FranzKugler/QlockThreeW32/src/LedDriverWS2812FastLED.cpp

/**
 * LedDriverWS2812FastLED
 * Implementation based on WS2812B strips, as used by the Adafruit NeoPixels.
 *
 * Adafruit's UeberGuide is well worth reading:
 * https://learn.adafruit.com/adafruit-neopixel-uberguide/overview
 *
 * @mc       ESP32S3
 * @author   Christian Aschoff / caschoff _AT_ mac _DOT_ com
 * @version  2.0
 * @created  5.1.2015
 * @updated  15.8.2026
 *
 * Version history:
 * V 1.0:  - Created.
 * V 1.1:  - Brightness getter brought in line.
 * V 1.2:  - Removed support for the old Arduino IDE (up to 1.0.6).
 * V 2.0:  - Consolidated for ESP32-S3 / WS2812B, comments translated to English.
 *
 * Wiring, from the owner of the clock and confirmed against the code and then
 * against the strip itself:
 *
 *     index 0    bottom right  (the R of the German panel)
 *     ...        meandering left, then up one row and back to the right
 *     index 109  top right     (the F)
 *     110..113   the corners: bottom right, top right, top left, bottom left
 *
 * This comment used to say "fed in at the top left, then serpentine downwards"
 * with the corners in a fourth order again, and all of it was wrong while the
 * code beneath it was right. It is restated here now because physicalFor()
 * gives the mapping a single home and /lab lets any claim about it be checked
 * in seconds - lighting cell (9,10) and lighting pixel 0 have to be the same
 * lamp, and now they can be seen to be.
 *
 * Which frame buffer row is which corner is still a separate question, because
 * the path there passes through _setPixel(), which swaps 110 with 112 on top
 * of the mapping in writeScreenBufferToMatrix. That one is written down at
 * Renderer::setCorners, from having been watched on the clock.
 *
 */
#include "LedDriverWS2812FastLED.h"

// #define DEBUG
// #include "Debug.h"

// Debug and the debugX macros, plus the ring the web UI reads them out of.
#include "LogBuffer.h"

#define NUM_PIXEL 114

/*
 * The four corner LEDs, named by where they are on the face rather than by
 * where they sit on the strip. Which frame buffer row is which corner is
 * written down at Renderer::setCorners and comes from the clock; these are
 * that mapping followed through _setPixel(), which swaps 110 with 112:
 *
 *     matrix[1] top left      -> _setPixel(110) -> _leds[112]
 *     matrix[0] top right     -> _setPixel(111) -> _leds[111]
 *     matrix[3] bottom right  -> _setPixel(112) -> _leds[110]
 *     matrix[2] bottom left   -> _setPixel(113) -> _leds[113]
 *
 * Only the coloured corners need them: that mode writes the pixels itself
 * instead of going through the frame buffer, so it has no rows to read.
 */
#define CORNER_TOP_LEFT     112
#define CORNER_TOP_RIGHT    111
#define CORNER_BOTTOM_RIGHT 110
#define CORNER_BOTTOM_LEFT  113

// The colour a corner settles on once the next one has lit; the newest one
// is the one that moves. Violet, on FastLED's rainbow wheel - which runs
// blue to purple over 160..191, not the cyan a geometric HSV would give.
//
// Note that the moving corner ends its minute at 3*59 = 177, just short of
// this, so in the last seconds of a minute the newest corner and the
// settled ones are nearly the same colour. That is how this mode has
// always behaved and is left alone.
#define CORNER_SETTLED_HUE 180

#ifndef LED_OUTPUT_PIN
	#define LED_OUTPUT_PIN 2
#endif

/**
 * Initialisation.
 *
 * @param data pin the data line is attached to.
 */
LedDriverWS2812FastLED::LedDriverWS2812FastLED(void)
{
	_leds = (CRGB*)malloc(NUM_PIXEL*sizeof(CRGB));
	//FastLED.addLeds<NEOPIXEL, 16>(_leds, NUM_PIXEL);
	
	FastLED.addLeds<NEOPIXEL, LED_OUTPUT_PIN>(_leds, NUM_PIXEL);
	FastLED.setMaxPowerInVoltsAndMilliamps(5, 2500);

	setColor(250, 255, 200);
	setColorCorners(false, true);
	updateFunkStatus(0);
}

/**
 * init() is called from the main program's init().
 * The LED driver should be brought into a defined
 * initial state here.
 */
/*
 * What the supply can give, minus room for the ESP32 and its radio.
 *
 * 114 WS2812B on white at full scale want about 6.8 A, which no sensible
 * supply for this clock provides - the normal face lights a fraction of them,
 * so it never comes up, but the lab interface can address every pixel and
 * would walk straight into it.
 *
 * Know how the cap works before trusting a measurement taken near it: FastLED
 * enforces it by scaling the *global* brightness down, so a frame over budget
 * is not the frame that was asked for. That is why /lab reports the estimated
 * draw beside every reading rather than only capping and staying quiet.
 */
#define SUPPLY_VOLTS 5
// 2.5 A of a 5 A supply. Measured: the normal face draws about 170 mA, so this
// never engages in use - it is a backstop against a lab frame, and it is set
// this low because 4 A was not: the first whole-face white frame browned the
// clock out and reset it. The real protection is LAB_MAX_DRAW_MW, which
// refuses such a frame instead of dimming it.
#define SUPPLY_MILLIAMPS 2500

void LedDriverWS2812FastLED::init()
{
	FastLED.setMaxPowerInVoltsAndMilliamps(SUPPLY_VOLTS, SUPPLY_MILLIAMPS);
	setBrightness(50);
	clearData();
	wakeUp();
}

void LedDriverWS2812FastLED::printSignature()
{
	debugI("FastLED - WS2812B on Pin %d\n", LED_OUTPUT_PIN);
}

/**
 * Write the frame buffer to the LED matrix.
 *
 * @param onChange TRUE if the frame buffer changed,
 *                  FALSE if this was a refresh call.
 */
void LedDriverWS2812FastLED::writeScreenBufferToMatrix(word matrix[16], boolean onChange)
{
	if (onChange || _dirty)
	{
		_dirty = false;
		FastLED.clear();

		CRGB color = CRGB(_brightnessScaleColor(getRed()), _brightnessScaleColor(getGreen()), _brightnessScaleColor(getBlue()));

		for (byte y = 0; y < 10; y++)
		{
			for (byte x = 5; x < 16; x++)
			{
				word t = 1 << x;
				if ((matrix[y] & t) == t)
				{
					_setPixel(15 - x, y, color);
				}
			}
		}

		if (!_colorCorners)
		{
			// The corner rows carry no letters, so they are handed to _setPixel
			// whole rather than column by column. Which row is which corner is
			// stated at Renderer::setCorners; the numbers below only have to
			// agree with it, and were checked against the clock.
			if ((matrix[1] & 0b0000000000011111) == 0b0000000000011111)
			{
				_setPixel(110, color); // top left
			}
			if ((matrix[0] & 0b0000000000011111) == 0b0000000000011111)
			{
				_setPixel(111, color); // top right
			}
			if ((matrix[3] & 0b0000000000011111) == 0b0000000000011111)
			{
				_setPixel(112, color); // bottom right
			}
			if ((matrix[2] & 0b0000000000011111) == 0b0000000000011111)
			{
				_setPixel(113, color); // bottom left
			}
		}
		else
		{
			/*
			 * The coloured corners. What each one shows is cornerHue()'s to
			 * say - this only puts it on the strip, at the same gamma the
			 * letters get.
			 *
			 * It cannot go through the frame buffer, because the hue differs
			 * per corner and a row of that buffer is one bit.
			 */
			const byte PIXEL[4] = {
				CORNER_TOP_LEFT, CORNER_TOP_RIGHT, CORNER_BOTTOM_RIGHT, CORNER_BOTTOM_LEFT
			};

			for (byte corner = 0; corner < 4; corner++)
			{
				byte hue;
				_leds[PIXEL[corner]] = cornerHue(corner, hue)
					? CHSV(hue, 255, _brightnessScaled)
					: CHSV(0, 0, 0);
			}
		}

		if (_funkStatus)
		{
			int brightness = _brightnessScaled;  // same gamma as the letters
			if ((_funkStatus & 0x0F) == 1)
				color = CHSV(96, 255, brightness); 
			else if ((_funkStatus & 0x0F) == 2)
				color = CHSV(0, 255, brightness); 
			else
				color = CHSV(0,0,0);
				
			if ((_funkStatus & 0x80) && (_second % 2))
				color = CHSV(0,0,0);

			_setPixel(3, 3, color);
			_setPixel(4, 3, color);
			_setPixel(5, 3, color);
			_setPixel(6, 3, color);
		}
		FastLED.show();
	}
}

void LedDriverWS2812FastLED::updateFunkStatus(byte status)
{
	_funkStatus = status;
}

/**
* Adjust the display colour.
*
* @param hue Hue
* @param sat Sat
*/
void LedDriverWS2812FastLED::setColorHS(byte hue, byte sat)
{
	CRGB pixel = CHSV(hue, sat, 255);
	setColor(pixel.r, pixel.g, pixel.b);
}


/**
 * Adjust the display brightness.
 *
 * @param brightnessInPercent the brightness.
 */
void LedDriverWS2812FastLED::setBrightness(byte brightnessInPercent)
{
	if (brightnessInPercent != _brightnessInPercent)
	{
		_brightnessInPercent = brightnessInPercent;
		_brightnessScaled = _gammaScale(brightnessInPercent);
		_dirty = true;
	}
}

/**
 * The setting as a drive value, with gamma.
 *
 * Perceived brightness follows roughly a power law, so driving the LEDs
 * proportionally to the setting does not feel proportional: half way up the
 * slider looked far brighter than half, and everything interesting happened in
 * the bottom third. Raising the setting to 2.2 spreads the useful range over
 * the whole slider.
 *
 * The floor matters as much as the curve: without it a setting of 1 to 3 per
 * cent rounds to zero and the clock goes dark while the web UI says it is on.
 */
byte LedDriverWS2812FastLED::_gammaScale(byte percent)
{
	if (percent == 0) return 0;
	if (percent >= 100) return 255;

	long value = lroundf(255.0f * powf(percent / 100.0f, 2.2f));
	if (value < 1) value = 1;
	return (byte)value;
}

/**
 * Get the current brightness.
 */
byte LedDriverWS2812FastLED::getBrightness()
{
	return _brightnessInPercent;
}

/**
 * Adjust the size of the frame buffer.
 *
 * @param linesToWrite how many rows of the frame buffer
 *                     should be written?
 */
void LedDriverWS2812FastLED::setLinesToWrite(byte linesToWrite)
{}

/**
 * Switch the display off.
 */
void LedDriverWS2812FastLED::shutDown()
{
	FastLED.clear();
	FastLED.show();
}

/**
 * Switch the display on.
 */
void LedDriverWS2812FastLED::wakeUp()
{}

/**
 * Clear the LED driver's data.
 */
void LedDriverWS2812FastLED::clearData()
{
	FastLED.clear();
	FastLED.show();
}

/**
 * Set a pixel in the matrix by x/y coordinate.
 */
void LedDriverWS2812FastLED::_setPixel(byte x, byte y, CRGB c)
{
	_setPixel((10 - x) + 11 * (9 - y), c);
}

/**
 * Where a letter cell sits on the strip - the wiring, worked out once.
 *
 * This is the same arithmetic _setPixel() does in two steps, gathered into one
 * place because the lab interface has to answer "which pixel is cell (r,c)"
 * and because the wiring had been described wrongly in three files. It is not
 * derived from the comment that used to sit at the top of this file; it is the
 * code that has always been driving the clock, checked against the owner's
 * description of the strip:
 *
 *     index 0   bottom right   ("R" on the German panel)
 *     ...       meandering left, then up one row and back to the right
 *     index 109 top right      ("F")
 *     110..113  the corners: bottom right, top right, top left, bottom left
 */
byte LedDriverWS2812FastLED::physicalFor(byte row, byte col)
{
	if (row > 9 || col > 10) return 255;

	// Reading order to strip order: the first cell is the bottom right one.
	byte num = (byte)((10 - col) + 11 * (9 - row));

	// Every other row runs the other way, which is what "meander" means.
	if ((num / 11) % 2 == 0) return num;
	return (byte)(((num / 11) * 11) + 10 - (num % 11));
}

void LedDriverWS2812FastLED::setPixelRaw(byte index, CRGB colour)
{
	if (index >= NUM_PIXEL) return;
	_leds[index] = colour;
}

CRGB LedDriverWS2812FastLED::getPixelRaw(byte index) const
{
	if (index >= NUM_PIXEL) return CRGB::Black;
	return _leds[index];
}

void LedDriverWS2812FastLED::clearRaw()
{
	for (byte i = 0; i < NUM_PIXEL; i++) _leds[i] = CRGB::Black;
}

void LedDriverWS2812FastLED::showRaw()
{
	// Marked dirty so that leaving the lab redraws the face from the frame
	// buffer even if nothing else changed in the meantime.
	_dirty = true;
	FastLED.show();
}

uint32_t LedDriverWS2812FastLED::estimatedDrawMilliwatts() const
{
	return calculate_unscaled_power_mW(_leds, NUM_PIXEL);
}

/**
 * Set a pixel in the strip (the corner LEDs come last).
 */
boolean LedDriverWS2812FastLED::cornerHue(byte corner, byte &hue) const
{
	/*
	 * What one corner shows in the coloured-corner mode, by its place on the
	 * face: 0 top left, 1 top right, 2 bottom right, 3 bottom left. That is
	 * reading order, and reading order is clockwise, so the order the corners
	 * light in is 0,1,2,3 one way and 1,0,3,2 the other - the same two
	 * sequences Renderer::setCorners uses, and for the same reason. Where a
	 * frame buffer row is which corner is written down there.
	 *
	 * The newest corner walks the hue wheel with the seconds and the ones
	 * before it sit still, so the moving one says roughly how far into the
	 * minute the clock is: red at :00 through to blue at :59.
	 *
	 * This is the answer to "what colour is that corner", and both askers get
	 * it from here - the strip, and GET /panel for the web UI's preview. The
	 * preview showed the plain display colour for a long time because it had
	 * no way to ask; a second implementation in the browser would have been
	 * the wrong fix.
	 *
	 * It counts the same minutes Renderer::setCorners does, which the hand
	 * written switch this replaced did not: a remainder of 0 lit a corner, so
	 * every corner came on a minute early and the fourth never went out.
	 */
	const byte CLOCKWISE[4]         = { 0, 1, 2, 3 };
	const byte COUNTER_CLOCKWISE[4] = { 1, 0, 3, 2 };
	const byte *order = _cw ? CLOCKWISE : COUNTER_CLOCKWISE;

	byte lit = _minute % 5;

	for (byte step = 0; step < 4; step++)
	{
		if (order[step] != corner) continue;

		if (step + 1 > lit) return false;                       // not yet
		hue = (step + 1 == lit) ? (byte)(3 * _second)           // the newest
		                        : (byte)CORNER_SETTLED_HUE;     // and settled
		return true;
	}

	return false;
}

void LedDriverWS2812FastLED::_setPixel(byte num, CRGB c)
{
	if (num < 110)
	{
		if ((num / 11) % 2 == 0)
		{
			_leds[num] = c;
		}
		else
		{
			_leds[((num / 11) * 11) + 10 - (num % 11)] = c;
		}
	}
	else
	{
		switch (num)
		{
		case 110:
			_leds[112] = c;
			break;
		case 111:
			_leds[111] = c;
			break;
		case 112:
			_leds[110] = c;
			break;
		case 113:
			_leds[113] = c;
			break;
		}
	}
}

/**
 * Function for clean 'rainbow' colours.
 * Copied from the Adafruit examples (strand).
 */
uint32_t LedDriverWS2812FastLED::_wheel(byte wheelPos)
{
	return 0;
}

/**
 * Helper for scaling the colours.
 */
byte LedDriverWS2812FastLED::_brightnessScaleColor(byte colorPart)
{
	return (byte)(((int)colorPart * (int)_brightnessScaled + 127) / 255);
}

void LedDriverWS2812FastLED::setColor(byte red, byte green, byte blue) {
    _red = red;
    _green = green;
    _blue = blue;
}

byte LedDriverWS2812FastLED::getRed() {
    return _red;
}

byte LedDriverWS2812FastLED::getGreen() {
    return _green;
}

byte LedDriverWS2812FastLED::getBlue() {
    return _blue;
}

void LedDriverWS2812FastLED::setPixelInScreenBuffer(byte x, byte y, word matrix[16]) {
    matrix[y] |= 0b1000000000000000 >> x;
}

boolean LedDriverWS2812FastLED::getPixelFromScreenBuffer(byte x, byte y, word matrix[16]) {
    return (matrix[y] & (0b1000000000000000 >> x)) == (0b1000000000000000 >> x);
}
