FranzKugler/QlockThreeW32/src/WebRoutes.cpp

/**
 * WebRoutes
 * The clock's HTTP interface: every handler the web UI talks to, plus the
 * state machine behind a network switch.
 *
 * That last one is not a route, but it belongs with them: POST /wifi only
 * records the request and answers immediately, because the response would
 * never leave the old network otherwise, and the switch itself then runs step
 * by step from loop(). Splitting the two halves apart would hide that.
 *
 * The /ota routes are not here - those come with the module that serves them,
 * see OtaUpdate.h. Neither are the /portal/* ones, reachable only before the
 * clock is on a network at all - see Portal.h - though Portal.cpp does reuse
 * this module's serveFromFilesystem() rather than a second copy.
 *
 * What this reaches for and does not own is listed below. It is a longer list
 * than OtaUpdate's, which is in the nature of the thing: these handlers exist
 * to read and write the clock's state.
 *
 * @mc       ESP32S3
 * @author   Franz Kugler / franz _AT_ franz _MINUS_ kugler _DOT_ de
 * @version  2.1
 * @created  17.8.2026
 * @updated  17.8.2026
 */
#include <Arduino.h>
#include <LittleFS.h>
#include <WiFi.h>
#include <WebServer.h>
#include <TimeLib.h>
#include <Timezone.h>
#include <ArduinoJson.h>
#include <esp_system.h>   // esp_reset_reason(), for the debug tab

#include "WebRoutes.h"
#include "OtaUpdate.h"   // a rename asks for a restart
#include "Settings.h"
#include "LightSensor.h"
#include "Expert.h"
#include "languages/Language.h"
#include "DisplayModes.h"
#include "LedDriverWS2812FastLED.h"   // the corner colours in sendPanel()
#include "Luminance.h"
#include "FactoryLuminance.h"
#include "Coupling.h"
#include "Calibration.h"
#include "Renderer.h"

// Debug and the debugX macros, plus the ring the web UI reads them out of.
#include "LogBuffer.h"

extern WebServer server;
extern Settings settings;
extern AmbientLight ambientLight;
extern bool wifiConnected;
// Cleared once the first connection has been dealt with; a network switch
// sets it again so loop() redoes what it does on a fresh connection.
extern bool wifiFirstConnected;

// The display mode in force, which POST /display sets. isKnownMode() comes
// from DisplayModes.h and is defined next to the render switch it guards.
extern byte mode;

// Set to have the face redrawn on the next pass through loop().
extern bool needsUpdateFromRtc;

// What the render loop last handed the LED driver. Reported beside the curve's
// own answer, because the two differ on purpose: while a nudge is being waited
// out the clock shows the nudge, and afterwards it eases towards the curve.
extern byte appliedBrightness;

// The frame buffer itself, and the sentence read back out of it. Both are
// owned by the render loop; /panel only ever looks.
extern word matrix[16];

// Only for the corner colours in sendPanel(): the coloured corners bypass
// the frame buffer, so the driver is the only place that knows them.
extern LedDriverWS2812FastLED ledDriver;
String displayedWords(byte language);

// Rebuilds the Timezone object after POST /timezone changed the rules.
void applyTimezoneFromSettings();

// Asks for the deferred settings write.
void scheduleSettingsSave();

// The NTP server in use, and the call that points SNTP at a new one.
extern String NTPServerName;
void startNtp();

// ------ Switching WiFi networks from the web UI ------
// A wrong password would otherwise lock us out of the network for good, so the
// switch runs as a state machine in loop(): try the new credentials, and fall
// back to the previous ones if they don't come up within WIFI_SWITCH_TIMEOUT.
#define WIFI_SWITCH_TIMEOUT 20000

enum WifiSwitchState {
    WIFI_SWITCH_IDLE,
    WIFI_SWITCH_START,      // request accepted, not acted on yet
    WIFI_SWITCH_WAIT_NEW,   // waiting for the new network
    WIFI_SWITCH_WAIT_OLD    // new one failed, waiting for the old one again
};

WifiSwitchState wifiSwitchState = WIFI_SWITCH_IDLE;
String wifiPendingSsid, wifiPendingPass;
String wifiPreviousSsid, wifiPreviousPass;
unsigned long wifiSwitchDeadline = 0;
// Empty unless the last switch failed. Holds a code, not a sentence: the web
// UI speaks six languages and translates it - see errorText() in errors.js.
String wifiLastError;
// The variable part of that message, e.g. the SSID. Never translated.
String wifiErrorDetail;


// ------ Webserver related functions ------

// convert the file extension to the MIME type
String getContentType(String filename) 
{ 
    if (filename.endsWith(".html"))     return "text/html";
    else if (filename.endsWith(".css")) return "text/css";
    else if (filename.endsWith(".js"))  return "application/javascript";
    else if (filename.endsWith(".json")) return "application/json";
    else if (filename.endsWith(".ico")) return "image/vnd.microsoft.icon";
    return "text/plain";
}

// send the right file to the client (if it exists)
bool Web::serveFromFilesystem(String path) 
{ 
    //Serial.println("Web::serveFromFilesystem: " + path);
    debugI("Web::serveFromFilesystem: %s", path.c_str());
    if (path.endsWith("/")) path += "index.html";           // If a folder is requested, send the index file
    String contentType = getContentType(path);              // Get the MIME type
    if (LittleFS.exists(path)) 
    {   // If the file exists
        File file = LittleFS.open(path, "r");                 // Open it
        server.streamFile(file, contentType);               // And send it to the client
        file.close();                                       // Then close the file again
        return true;
    }
    debugE("\tFile Not Found");
    return false;                                           // If the file doesn't exist, return false
}

// when the index.html page is loaded, this is called to send the actual settings for a correct display
void sendCurrentState()
{
    server.send(200, "application/json", settings.getJSONSettings());
}

/**
 * True for a mode the render switch still has a case for.
 *
 * Guards both the request and the stored value: a clock updating from a build
 * that still offered the uptime display has 4 in NVS, and without this it
 * would land in the switch, match nothing, and leave whatever was in the frame
 * buffer on the face.
 */

void updateDisplay()
{
    JsonDocument doc;
    deserializeJson(doc, server.arg(0));
    byte wanted = doc["display"] | STD_MODE_NORMAL;
    mode = isKnownMode(wanted) ? wanted : STD_MODE_NORMAL;
    settings.setMode(mode);

    needsUpdateFromRtc = true;
    scheduleSettingsSave();

    server.send(200, "application/json", "{\"msg\":\"\"}");
}

// switch on / off auto luminance functionality
void updateAutoLuminance()
{
    JsonDocument doc;
    deserializeJson(doc, server.arg(0));
    settings.setUseLdr(doc["automaticLum"].as<int>());

    
    needsUpdateFromRtc = true;
    scheduleSettingsSave();

    server.send(200, "application/json", "{\"msg\":\"\"}");
}

/**
 * Colour and brightness.
 *
 * The brightness slider has two meanings. With the automatic off it is the
 * brightness, stored and kept. With it on it is "at this light, I want this
 * much" - the automatic steps aside, and ten seconds after the last move the
 * pair is kept and the line re-fitted; see Luminance.h. The stored manual
 * brightness is deliberately left alone in that case, so switching the
 * automatic off gives back the value chosen by hand rather than the last thing
 * the learning was told.
 *
 * The settle timer lives here rather than in the browser, because a tab closed
 * mid-adjustment must not lose the point.
 */
void updateColor()
{
    JsonDocument doc;
    deserializeJson(doc, server.arg(0));

    // Each of the three is optional, and a missing one means "leave this
    // alone". That is not politeness, it is the only way the three can be set
    // independently - and every one of them had a real fault before:
    //
    //  - a body without `hue` set the hue to zero, which is red;
    //  - a body without `lum` set the brightness to zero, which is a dark
    //    clock that the web UI still shows as lit;
    //  - and a body *with* an unchanged `lum` was read as somebody adjusting
    //    the brightness, so dragging the colour wheel taught the automatic a
    //    calibration point nobody asked for. The tab sent all three on every
    //    change because there was no way to send fewer.
    //
    // Stored in the units they arrive in; the renderer scales them to 8 bit.
    if (!doc["hue"].isNull()) settings.setColorHue((uint16_t)doc["hue"].as<int>());
    if (!doc["sat"].isNull()) settings.setColorSat((byte)doc["sat"].as<int>());

    if (doc["lum"].isNull())
    {
        // Colour only. Nothing about the brightness was said, so nothing about
        // the brightness is changed and nothing is learned.
        needsUpdateFromRtc = true;
        scheduleSettingsSave();
        server.send(200, "application/json", "{\"msg\":\"\"}");
        return;
    }

    if (settings.getUseLdr() && ambientLight.present())
    {
        // is<int>() was too strict, and failed silently: "lum": "55" went
        // nowhere while the manual branch below converted it happily, so the
        // automatic looked broken in exactly the way it did not deserve.
        // The colour travels with the brightness, because that is the face the
        // person was looking at when they decided what it should be worth. See
        // Luminance::Point.
        Luminance::nudged((byte)doc["lum"].as<int>(),
                          settings.getColorHue(), settings.getColorSat());
    }
    else
    {
        settings.setBrightness((byte)doc["lum"].as<int>());
    }

    needsUpdateFromRtc = true;
    scheduleSettingsSave();
    
    server.send(200, "application/json", "{\"msg\":\"\"}");
}

/**
 * Language and the corner LED options.
 *
 * Once the clock is set up, the language may only move within the panel it
 * already has. The panel is a milled sheet of letters, not a setting: on an
 * Italian clock every other language is a wall of letters that spells nothing,
 * and whoever changed it by accident has no way of knowing what went wrong.
 * Expert mode is where a clock is set up; normal mode is where it can no
 * longer be set up wrongly.
 *
 * "Set up" means enrolled - a password has been chosen. A clock with none is
 * left alone, and that is not the same inconsistency it looks like next to
 * Expert::guard(), which closes /log and /ota/* on such a clock too. Those two
 * keep a stranger on the network out. This one keeps the owner from breaking
 * their own face, and someone who has not yet declared the clock set up is
 * still setting it up. Locking them out of the one setting that has to match
 * the hardware would be the worst moment to start.
 *
 * Guarded here rather than only in the browser, for the same reason the expert
 * tabs are: the endpoint is reachable without the UI. And guarded by the
 * *stored* language, not by anything the request says about it.
 */
void updateConfiguration()
{
    JsonDocument doc;
    deserializeJson(doc, server.arg(0));

    byte wanted = (byte)doc["language"].as<int>();
    if (Expert::enrolled() && !Expert::unlocked() && wanted != settings.getLanguage())
    {
        const Language *have = Languages::find(settings.getLanguage());

        // A stored language this firmware does not know says nothing about
        // which panel is on the wall, so it cannot be grounds for a refusal.
        if (have != nullptr && !Languages::samePanel(have, Languages::find(wanted)))
        {
            server.send(403, "application/json", "{\"error\":\"languageNotOnPanel\"}");
            return;
        }
    }

    settings.setLanguage(wanted);
    settings.setRenderCornersCw(doc["cornerDirection"].as<int>());
    settings.setRenderColorCorner(doc["cornerColor"].as<int>());
    
    needsUpdateFromRtc = true;
    scheduleSettingsSave();
    
    server.send(200, "application/json", "{\"msg\":\"\"}");
}

/**
 * One changeover rule, built from the stored fields.
 *
 * TimeChangeRule is {abbrev, week, dow, month, hour, offset}. Filling it
 * positionally is what the six call sites used to do, with month and dow the
 * wrong way round - a month number landed in the day-of-week field, where 10
 * is not a weekday at all, and the resulting changeover date was meaningless.
 * Naming the fields here means the order is stated once.
 */

void updateTimezone()
{
    JsonDocument doc;
    deserializeJson(doc, server.arg(0));
    settings.setNTPServer(doc["ntpServer"].as<const char*>());
    settings.setUseDs(doc["useDs"].as<bool>());
    settings.setTzName(doc["tzName"].as<const char*>());
    settings.setTzWeek(doc["tzWeek"].as<unsigned char>());
    settings.setTzMonth(doc["tzMonth"].as<unsigned char>());
    settings.setTzDoW(doc["tzDoW"].as<unsigned char>());
    settings.setTzHour(doc["tzHour"].as<unsigned char>());
    settings.setTzOffset(doc["tzOffset"].as<int>());
    settings.setTzDsName(doc["tzDsName"].as<const char*>());
    settings.setTzDsWeek(doc["tzDsWeek"].as<unsigned char>());
    settings.setTzDsMonth(doc["tzDsMonth"].as<unsigned char>());
    settings.setTzDsDoW(doc["tzDsDoW"].as<unsigned char>());
    settings.setTzDsHour(doc["tzDsHour"].as<unsigned char>());
    settings.setTzDsOffset(doc["tzDsOffset"].as<int>());

    // Which entry of the zone list the rules came from, so the web UI can show
    // it again after a reload. Purely a label - the rules above are what the
    // clock runs on. Absent in a request from an older web UI, which must not
    // clear a name that is already stored.
    if (doc["tzZone"].is<const char*>()) settings.setTzZone(doc["tzZone"].as<const char*>());

    applyTimezoneFromSettings();

    // if timeserver address changed
    if (NTPServerName != String(settings.getNTPServer()))
    {
        debugI("Timeserver changed from %s to %s", NTPServerName.c_str(), settings.getNTPServer());
        NTPServerName = String(settings.getNTPServer());
        startNtp();
    }

    needsUpdateFromRtc = true;
    scheduleSettingsSave();
    
    server.send(200, "application/json", "{\"msg\":\"\"}");       
}

// ------ WiFi endpoints for the web UI ------

/**
 * Reduces a requested name to something usable as a DNS label: letters, digits
 * and hyphens, no hyphen at either end, at most 32 characters. Returns an empty
 * string when nothing is left, which the caller rejects.
 *
 * Done here rather than trusted from the browser - the endpoint is reachable
 * without going through the UI, and a name with a dot or a space in it would
 * produce an mDNS record nobody can reach.
 */
String sanitizeHostname(const String& wanted)
{
    String clean;
    for (unsigned int i = 0; i < wanted.length() && clean.length() < 32; i++)
    {
        char c = wanted.charAt(i);
        if (isalnum((unsigned char)c) || c == '-') clean += c;
    }
    while (clean.length() && clean.charAt(0) == '-') clean.remove(0, 1);
    while (clean.length() && clean.charAt(clean.length() - 1) == '-') clean.remove(clean.length() - 1);
    return clean;
}

/**
 * Renames the clock and restarts it.
 *
 * A restart because the name is read in six places and only mDNS can be
 * changed while the clock runs - the DHCP name, the OTA name and the setup
 * access point are all read as the interface comes up. Renaming without one
 * left the clock answering to two different names depending on who was asking.
 *
 * The settings go to NVS here and now rather than through the deferred write,
 * which would still be pending when the restart happens and would lose the new
 * name. The answer carries the name that was actually stored, which is not
 * necessarily the one that was asked for.
 */
void updateHostname()
{
    JsonDocument doc;
    deserializeJson(doc, server.arg(0));

    String wanted = sanitizeHostname(doc["hostname"] | "");
    if (wanted.length() == 0)
    {
        server.send(400, "application/json", "{\"error\":\"hostnameInvalid\"}");
        return;
    }

    JsonDocument answer;
    answer["hostname"] = wanted;
    answer["restarting"] = (wanted != String(settings.getHostname()));
    String out;
    serializeJson(answer, out);

    if (wanted != String(settings.getHostname()))
    {
        settings.setHostname(wanted.c_str());
        settings.storeSettings();
        debugA("Renamed to %s, restarting", settings.getHostname());

        // Answer first, then restart from loop() - the response would never
        // reach the browser otherwise. Nothing else is pending: the write above
        // has already happened.
        server.send(200, "application/json", out);
        Ota::scheduleRestart();
        return;
    }

    server.send(200, "application/json", out);
}

/**
 * Restarts the clock, and nothing else.
 *
 * It exists for one situation, which is the storage tab: the firmware holds
 * its records in RAM and writes them back on the next settings change, so an
 * edit made to `qlock/conf` in NVS is only durable if the clock is restarted
 * before anything else touches it. Saying that in a warning and then leaving
 * the reader to find a power socket would be telling half the story.
 *
 * Behind the lock like the tab it serves. `/hostname` restarts without a guard
 * and predates it; there is no reason for a new reboot button to be open to
 * whoever is on the network.
 *
 * The answer goes out first and the restart happens in loop() through the same
 * Ota::scheduleRestart() a rename uses - it is not an update, but it needs
 * exactly the same delay, or the response never reaches the browser.
 */
void restartClock()
{
    if (!Expert::guard()) return;

    debugA("Restart asked for over HTTP");
    server.send(200, "application/json", "{\"restarting\":true}");
    Ota::scheduleRestart();
}

/**
 * The web app manifest, which is how Android decides what to put on a home
 * screen - it ignores the apple-touch-icon iOS uses.
 *
 * Served from here rather than shipped as a file in the filesystem image,
 * because the manifest carries the app name and that is per clock. The
 * alternative, building it in the browser and handing Chrome a blob: URL,
 * works but depends on behaviour that has changed between versions; a real
 * response from the clock does not.
 *
 * The icons themselves are static files and do come from the image.
 */
void sendManifest()
{
    JsonDocument doc;
    doc["name"] = settings.getHostname();
    doc["short_name"] = settings.getHostname();
    doc["start_url"] = "/";
    doc["display"] = "standalone";
    doc["background_color"] = "#0d0d0d";
    doc["theme_color"] = "#0d0d0d";

    JsonArray icons = doc["icons"].to<JsonArray>();

    JsonObject small = icons.add<JsonObject>();
    small["src"] = "/icon-192.png";
    small["sizes"] = "192x192";
    small["type"] = "image/png";

    JsonObject large = icons.add<JsonObject>();
    large["src"] = "/icon-512.png";
    large["sizes"] = "512x512";
    large["type"] = "image/png";

    // Declared separately because it is drawn with a wider margin: a launcher
    // may crop a maskable icon to any shape inside the middle 80 %.
    JsonObject maskable = icons.add<JsonObject>();
    maskable["src"] = "/icon-512-maskable.png";
    maskable["sizes"] = "512x512";
    maskable["type"] = "image/png";
    maskable["purpose"] = "maskable";

    String out;
    serializeJson(doc, out);
    server.send(200, "application/manifest+json", out);
}

/**
 * What the light sensor sees. Polled by the colour tab while it is open, which
 * is why it carries the raw reading as well as the smoothed one: placing the
 * sensor behind the front panel is a matter of watching the raw number while
 * moving it, and the smoothed one lags half a minute behind on purpose.
 */
void sendLight()
{
    JsonDocument doc;
    doc["sensor"]    = ambientLight.name();
    doc["present"]   = ambientLight.present();
    doc["available"] = ambientLight.available();
    doc["lux"]       = ambientLight.lux();
    doc["raw"]       = ambientLight.raw();

    // What the clock's own face contributed to that raw reading, and how many
    // cells the map describes. `raw` minus `display` is what the averages were
    // fed - without the middle number the two would look like a sensor fault
    // rather than a correction. Zero cells means no map is stored and nothing
    // is being subtracted, which is a different thing from a dark face.
    doc["display"]   = ambientLight.own();
    doc["coupled"]   = Coupling::cells();

    // The line, and what it makes of the current reading. The UI shows that
    // number beside the slider: with the automatic on the slider is not what
    // the display is doing, and a control that lies is worse than no control.
    doc["slope"]      = Luminance::slope();
    doc["offset"]     = Luminance::offset();
    doc["fitted"]     = Luminance::slopeFitted();
    doc["brightness"] = Luminance::forLux(ambientLight.lux());
    doc["applied"]    = appliedBrightness;
    doc["minPercent"] = Luminance::minPercent();
    doc["maxPercent"] = Luminance::maxPercent();

    // How much the clock has been told. The colour tab only needs the count;
    // the points themselves are GET /luminance's business.
    Luminance::Point kept[LUM_POINTS];
    doc["taught"] = Luminance::points(kept, LUM_POINTS);

    // Whether a nudge is being waited out, so the slider can stay where it was
    // put instead of snapping back to the curve for ten seconds.
    byte nudge;
    doc["adjusting"] = Luminance::adjusting(nudge);

    String out;
    serializeJson(doc, out);
    server.send(200, "application/json", out);
}

/**
 * The only thing left to write about the brightness curve: throw it away.
 *
 *   {reset: true}   forget every point, back to the default line
 *
 * There is nothing else to set. The curve is not configured any more, it is
 * taught - by moving the brightness slider while the automatic is on, which
 * arrives at POST /color like any other slider move. Luminance.h says why that
 * is the whole interface.
 *
 * What used to be here - two calibration points to POST, and a {want} that
 * shifted the level while keeping the slope - is gone. The shift survives, but
 * as the fallback for points too close together to carry a slope, which is the
 * only case where sliding the whole line is the honest answer.
 */
void updateLight()
{
    JsonDocument doc;
    deserializeJson(doc, server.arg(0));

    if (doc["reset"] | false)
    {
        Luminance::reset();
        needsUpdateFromRtc = true;
        sendLight();
        return;
    }

    // The coupling map, as scripts/lab.py measures it. Behind the lock while
    // the reset above is not, and the difference is real: a reset throws away
    // what the clock has been told and can be told again, while this changes
    // how the clock reads its own sensor for good. It is also the one thing
    // here nobody types by hand.
    if (!doc["coupling"].isNull())
    {
        if (!Expert::guard()) return;

        String map;
        serializeJson(doc["coupling"], map);
        if (!Coupling::store(map))
        {
            server.send(400, "application/json", "{\"error\":\"couplingInvalid\"}");
            return;
        }
        sendLight();
        return;
    }

    if (doc["couplingReset"] | false)
    {
        if (!Expert::guard()) return;
        Coupling::reset();
        sendLight();
        return;
    }

    // The clock measuring the map itself, rather than being handed one. Here
    // beside the upload rather than on /luminance, because what it produces is
    // the same thing the upload writes; the progress is reported in
    // /luminance, which is the screen that shows it.
    if (doc["calibrate"] | false)
    {
        if (!Expert::guard()) return;
        if (!Calibration::start())
        {
            String out = "{\"error\":\"";
            out += Calibration::error();
            out += "\"}";
            server.send(409, "application/json", out);
            return;
        }
        sendLight();
        return;
    }

    if (doc["calibrateAbort"] | false)
    {
        if (!Expert::guard()) return;
        Calibration::cancel();
        sendLight();
        return;
    }

    server.send(400, "application/json", "{\"error\":\"calibrationRange\"}");
}

/**
 * The colour-aware model, as much of it as a screen needs.
 *
 * Three separate things, and they are separate because their remedies are:
 * **which profile** is installed (identity, and whether the corrections in
 * NVS were learned on it), **what it is worth** (the acceptance figures it was
 * measured to, carried rather than hidden - the reviewed profile misses its
 * goal at one hue and a clock that omitted that would be claiming an accuracy
 * nobody measured), and **what it says right now** in the colour the face is
 * actually showing.
 *
 * What is not here is the measurement. The cone, the nose, blue's line and
 * the drive table change only on a filesystem update; the diagram fetches
 * them once from /luminance/surface. Putting them in a response polled once a
 * second would be sending a constant over and over on a synchronous web
 * server.
 */
static void describeFactory(JsonDocument &doc)
{
    JsonObject factory = doc["factory"].to<JsonObject>();
    factory["valid"]   = FactoryLuminance::available();
    factory["error"]   = FactoryLuminance::error();
    factory["profileId"] = FactoryLuminance::profileId();
    factory["stackId"]   = FactoryLuminance::stackId();
    factory["checksum"]  = FactoryLuminance::sourceChecksum();

    // Whether the raw observations behind the fit rose with light - see
    // FactoryLuminance.h. The fit itself is monotone by construction
    // (FactoryProfile::valid()), so there is no second, model-side answer to
    // report beside it any more.
    factory["observationsMonotone"] = FactoryLuminance::observationsMonotone();

    factory["acceptanceMet"] = FactoryLuminance::acceptanceMet();
    factory["maxError"]      = FactoryLuminance::maxError();
    factory["worstHue"]      = FactoryLuminance::worstHue();

    // Which profile the stored corrections belong to. A filesystem update can
    // bring a new measurement underneath them, and adding a correction learned
    // on one baseline to another is arithmetic across two models.
    // Two different facts that used to be one. `recorded` is the profile NVS
    // says this clock is on, written once; `matched` is whether the
    // corrections in hand were learned about the profile now installed - and
    // on a clock that has never corrected anything nothing disagrees, which is
    // not the same as "no". See Luminance::residualsStale().
    factory["recorded"] = FactoryLuminance::recordedChecksum();
    factory["matched"]  = !Luminance::residualsStale();

    if (FactoryLuminance::available())
    {
        const FactoryProfile::Profile &model = FactoryLuminance::profile();
        factory["huePeriod"] = model.huePeriod;
        factory["coneSlope"] = model.coneSlope;
        factory["coneOffset"] = model.coneOffset;
        factory["luxMin"] = pow(10.0, model.logLuxMin);
        factory["luxMax"] = pow(10.0, model.logLuxMax);
        factory["blueHue"] = model.blueHue;
        factory["blendHalfWidth"] = model.blendHalfWidth;

        // The shipped nose and blue's line, as measured - shown beside
        // `user.fit` below rather than only kept internally, because "what
        // the fit actually is" is exactly the number somebody reaching for
        // the geek section wants, not only what it predicts at one hue.
        factory["noseA0"] = model.noseA0;
        factory["noseA1"] = model.noseA1;
        factory["noseB1"] = model.noseB1;
        factory["blueSlope"] = model.blueSlope;
        factory["blueOffset"] = model.blueOffset;
    }

    // What it asks for here, now, in the colour on the face - and what the
    // grid alone asked for beside it, because "the model says 42 and you have
    // taught it 47" is the sentence somebody needs when the automatic feels
    // wrong.
    Luminance::Target wanted;
    Luminance::targetFor(ambientLight.lux(), settings.getColorHue(),
                         settings.getColorSat(), wanted);
    JsonObject target = doc["target"].to<JsonObject>();
    target["percent"] = wanted.percent;
    target["factory"] = wanted.factory;
    target["bias"]    = wanted.bias;
    target["hue"]     = settings.getColorHue();
    target["sat"]     = settings.getColorSat();
    target["limited"] = wanted.limited;
    target["bound"]   = wanted.bound;
    target["clamped"] = wanted.clamped;
    target["source"]  = wanted.source == Luminance::SOURCE_FACTORY_USER ? "factory+user"
                      : wanted.source == Luminance::SOURCE_FACTORY ? "factory"
                      : "legacy";

    // The corrections themselves: few, small, and the thing somebody wants to
    // forget one of when the clock has learned something silly.
    Luminance::Residual kept[LUM_USER_POINTS];
    uint8_t held = Luminance::residuals(kept, LUM_USER_POINTS);
    JsonObject user = doc["user"].to<JsonObject>();
    user["capacity"] = LUM_USER_POINTS;
    JsonArray list = user["residuals"].to<JsonArray>();
    for (uint8_t i = 0; i < held; i++)
    {
        JsonObject one = list.add<JsonObject>();
        one["lux"]     = pow(10.0, kept[i].logLux);
        one["decades"] = kept[i].decades;
        one["hue"]     = kept[i].hue;
        one["sat"]     = kept[i].sat;
        one["seconds"] = kept[i].seconds;
        // Whether the slider had anything left to give. "At least this much"
        // is a weaker statement than "exactly this much" and the screen has to
        // be able to say which one it is holding - a correction that reads as
        // exact while the model quietly treats it as a bound is the worst of
        // both. See ResidualStore::Residual::bound.
        one["bound"]   = kept[i].bound != 0;

        // Where this statement sits on the sat-100 surface the diagram draws -
        // computed here, not in the browser, for the same reason the surface
        // itself is: the conversion from a decades residual to a percentage is
        // the inversion FactoryProfile::evaluate already does, and a second
        // implementation in JavaScript would be exactly the kind of drift this
        // project's own rule warns against. White has no hue and is left off a
        // diagram whose one axis is hue.
        //
        // Two calls rather than one: evaluate() first, to read off what the
        // model itself would say at this hue (`plain.residual`), then
        // evaluateWith() with the gap between that and what was actually
        // taught folded in as `bias` - which lands the target exactly on
        // `white + decades`, the taught statement itself, rather than on
        // `white + decades + the model's own opinion` counted twice.
        if (FactoryLuminance::available() && kept[i].sat > 0)
        {
            const FactoryProfile::Profile &model = FactoryLuminance::profile();
            double lux = pow(10.0, kept[i].logLux);
            FactoryProfile::Answer plain, taught;
            if (FactoryProfile::evaluate(model, lux, kept[i].hue, 100, plain)
                && FactoryProfile::evaluateWith(model, lux, kept[i].hue, 100,
                                                kept[i].decades - plain.residual, taught))
            {
                one["percent"] = taught.percent;
            }
        }
    }

    // What the taught points above actually made of the nose and blue's line -
    // the numbers `refit()` produced, not only what they predict at one hue.
    // Absent rather than equal to the factory's own when nothing has been
    // taught about a colour yet: a fit that quietly repeats the factory
    // numbers would look like a second, redundant measurement rather than
    // "there is nothing to show here yet".
    ResidualStore::Fit fit;
    if (Luminance::learnedFit(fit))
    {
        JsonObject learned = user["fit"].to<JsonObject>();
        learned["noseA0"] = fit.noseA0;
        learned["noseA1"] = fit.noseA1;
        learned["noseB1"] = fit.noseB1;
        learned["blueSlope"] = fit.blueSlope;
        learned["blueOffset"] = fit.blueOffset;
    }
}

/**
 * The surface the diagram draws: a percentage for every knot and every hue.
 *
 * Computed here rather than in the browser, and that is the same rule the face
 * preview follows - the browser is not a second opinion. Rebuilding the
 * inversion in JavaScript would be a second implementation of the one thing
 * the golden vectors exist to pin down, and it would hide exactly the faults
 * worth seeing.
 *
 * At saturation 100, because that is where the colour residual is whole and
 * therefore where the surface has any shape at all; at sat 0 it is a flat
 * sheet and says nothing. The hue axis is walked at a finer step than the
 * knots so the seam at 300 -> 0 is drawn rather than implied.
 *
 * Fetched once. It changes when the profile changes, which is when the
 * filesystem image changes, which is a reboot away.
 */
void sendLuminanceSurface()
{
    JsonDocument doc;
    doc["valid"] = FactoryLuminance::available();
    doc["error"] = FactoryLuminance::error();

    if (!FactoryLuminance::available())
    {
        String out;
        serializeJson(doc, out);
        server.send(200, "application/json", out);
        return;
    }

    const FactoryProfile::Profile &model = FactoryLuminance::profile();
    doc["profileId"] = FactoryLuminance::profileId();
    doc["checksum"]  = FactoryLuminance::sourceChecksum();
    doc["sat"]       = 100;
    doc["minPercent"] = Luminance::minPercent();
    doc["maxPercent"] = Luminance::maxPercent();

    // The cone has no ambient rows of its own - it is a straight line - so
    // LUM_SURFACE_LUX_ROWS of them are chosen, evenly spaced in log light
    // over what the fit was actually built from. See Luminance.h.
    double logLuxMin = model.logLuxMin, logLuxSpan = model.logLuxMax - model.logLuxMin;
    JsonArray luxes = doc["lux"].to<JsonArray>();
    for (uint8_t i = 0; i < LUM_SURFACE_LUX_ROWS; i++)
    {
        double logLux = logLuxMin + logLuxSpan * i / (double)(LUM_SURFACE_LUX_ROWS - 1);
        luxes.add(pow(10.0, logLux));
    }

    JsonArray hues = doc["hue"].to<JsonArray>();
    for (int hue = 0; hue < model.huePeriod; hue += LUM_SURFACE_HUE_STEP) hues.add(hue);

    // Row per ambient level, column per hue. Two parallel grids rather than
    // objects per cell: the percentages are what is drawn, `limited` is what
    // is shaded - a reader of `curl` output can line them up, and the
    // response stays a few hundred bytes rather than a few thousand. There is
    // no third grid any more: the parametric fit carries no per-cell "at
    // least this much" the way the grid it replaced did.
    JsonArray percent = doc["percent"].to<JsonArray>();
    JsonArray limited = doc["limited"].to<JsonArray>();
    for (uint8_t i = 0; i < LUM_SURFACE_LUX_ROWS; i++)
    {
        double logLux = logLuxMin + logLuxSpan * i / (double)(LUM_SURFACE_LUX_ROWS - 1);
        double lux = pow(10.0, logLux);
        JsonArray row = percent.add<JsonArray>();
        JsonArray limitedRow = limited.add<JsonArray>();
        for (int hue = 0; hue < model.huePeriod; hue += LUM_SURFACE_HUE_STEP)
        {
            FactoryProfile::Answer answer;
            if (!FactoryProfile::evaluate(model, lux, (uint16_t)hue, 100, answer))
            {
                row.add(0);
                limitedRow.add(false);
                continue;
            }
            row.add(answer.percent);
            limitedRow.add(answer.limited != FactoryProfile::LIMITED_NONE);
        }
    }

    String out;
    serializeJson(doc, out);
    server.send(200, "application/json", out);
}

/**
 * Everything the automatic brightness is thinking, for a human.
 *
 * Reached at #luminance in the web UI, with no chip in the tab row - it is a
 * workbench, not a setting. Deliberately **not** behind expert mode: there is
 * no secret in it, and needing to unlock the clock to look at a brightness
 * curve would put a lock in the way of something it has nothing to do with.
 * Reading it is open; the writes beside it are not. See updateLuminance().
 */
void sendLuminance()
{
    JsonDocument doc;
    doc["lux"]        = ambientLight.lux();
    doc["raw"]        = ambientLight.raw();
    doc["available"]  = ambientLight.available();

    // Both averages, because they answer different questions and a point kept
    // against the wrong one is the failure this pair was split to prevent.
    // `lux` regulates, `teaching` is what a nudge would be stored against.
    doc["teaching"]   = ambientLight.teachingLux();

    // The other half of the automatic, and the reason this screen exists as
    // more than a chart: how much of the raw reading was the clock's own face,
    // and over how many cells that is known. See Coupling.h.
    doc["display"]    = ambientLight.own();
    doc["coupled"]    = Coupling::cells();

    // Where a self-calibration has got to. In this response and not in a
    // polling endpoint of its own, because this is the screen that starts one
    // and it already asks once a second - a second poller would only be a
    // second answer to disagree with. `phase` is Calibration::Phase; `error`
    // carries a code from the same vocabulary as any other failed write.
    JsonObject calib = doc["calibration"].to<JsonObject>();
    calib["running"] = Calibration::running();
    calib["phase"]   = (uint8_t)Calibration::phase();
    calib["done"]    = Calibration::done();
    calib["total"]   = Calibration::total();
    calib["ambient"] = Calibration::ambient();
    calib["rung"]    = Calibration::rung();
    calib["kept"]    = Calibration::kept();
    calib["error"]   = Calibration::error();
    calib["maxAmbient"] = CAL_MAX_AMBIENT_LUX;

    doc["slope"]      = Luminance::slope();
    doc["offset"]     = Luminance::offset();
    doc["fitted"]     = Luminance::slopeFitted();
    doc["brightness"] = Luminance::forLux(ambientLight.lux());
    doc["applied"]    = appliedBrightness;
    doc["minPercent"] = Luminance::minPercent();
    doc["maxPercent"] = Luminance::maxPercent();
    doc["capacity"]   = LUM_POINTS;
    doc["settleMs"]   = LUM_SETTLE_MS;
    doc["uptime"]     = (uint32_t)(millis() / 1000);

    // The colour-aware model: which one is installed, whether it may be acted
    // on, and what it asks for right now in the colour the face is showing.
    // Deliberately compact - the identity and the axes, not the measurement.
    // The 43 KB of provenance stays in `artifacts/`, and the surface the
    // diagram draws has an endpoint of its own because it is fetched once
    // while this is polled every second.
    describeFactory(doc);

    byte nudge;
    bool busy = Luminance::adjusting(nudge);
    doc["adjusting"] = busy;
    if (busy) doc["wanted"] = nudge;

    // Oldest first, each with what the line makes of its own light - which is
    // the number worth looking at, because it says how far the fit ended up
    // from what was actually asked for at that point.
    Luminance::Point kept[LUM_POINTS];
    uint8_t taught = Luminance::points(kept, LUM_POINTS);
    JsonArray list = doc["points"].to<JsonArray>();
    for (uint8_t i = 0; i < taught; i++)
    {
        JsonObject one = list.add<JsonObject>();
        // Whether it was in the fit at all: a point at the top of the range
        // is censored and left out, and one that is shown but silently
        // ignored is worse than one that is not shown.
        one["used"]    = Luminance::usedInFit(i);
        // Absent rather than null when the point predates the colour being
        // kept: a reader can then tell "taught in red" from "we do not know".
        if (kept[i].hue != LUM_HUE_UNKNOWN)
        {
            one["hue"] = kept[i].hue;
            one["sat"] = kept[i].sat;
        }
        one["lux"]     = kept[i].lux;
        one["percent"] = kept[i].percent;
        one["seconds"] = kept[i].seconds;
        one["curve"]   = Luminance::forLux(kept[i].lux);
    }

    String out;
    serializeJson(doc, out);
    server.send(200, "application/json", out);
}

// Current connection, plus the outcome of a switch requested via POST /wifi.
void sendWifiStatus()
{
    JsonDocument doc;
    doc["connected"] = (WiFi.status() == WL_CONNECTED);
    doc["ssid"]      = WiFi.SSID();
    doc["ip"]        = WiFi.localIP().toString();
    doc["rssi"]      = WiFi.RSSI();
    doc["mac"]       = WiFi.macAddress();
    doc["hostname"]  = settings.getHostname();
    doc["switching"] = (wifiSwitchState != WIFI_SWITCH_IDLE);
    doc["error"]       = wifiLastError;
    doc["errorDetail"] = wifiErrorDetail;

    String out;
    serializeJson(doc, out);
    server.send(200, "application/json", out);
}

// Async scan: the first call kicks one off, the web UI polls until it is done.
void sendWifiScan()
{
    JsonDocument doc;
    int found = WiFi.scanComplete();

    if (found == WIFI_SCAN_RUNNING)
    {
        doc["scanning"] = true;
    }
    else if (found == WIFI_SCAN_FAILED)
    {
        // Nothing running and nothing cached: start one.
        WiFi.scanNetworks(true);
        doc["scanning"] = true;
    }
    else
    {
        doc["scanning"] = false;
        JsonArray networks = doc["networks"].to<JsonArray>();
        for (int i = 0; i < found && i < 20; i++)
        {
            JsonObject net = networks.add<JsonObject>();
            net["ssid"]   = WiFi.SSID(i);
            net["rssi"]   = WiFi.RSSI(i);
            net["secure"] = (WiFi.encryptionType(i) != WIFI_AUTH_OPEN);
        }
        // Drop the cache so the next poll starts a fresh scan.
        WiFi.scanDelete();
    }

    String out;
    serializeJson(doc, out);
    server.send(200, "application/json", out);
}

// Accepts new credentials and answers immediately - the actual switch happens
// in loop(), otherwise the response would never make it out of the old network.
void updateWifi()
{
    JsonDocument doc;
    deserializeJson(doc, server.arg("plain"));

    wifiPendingSsid = doc["ssid"].as<const char*>();
    wifiPendingPass = doc["password"] | "";

    if (wifiPendingSsid.length() == 0)
    {
        server.send(400, "application/json", "{\"error\":\"ssid missing\"}");
        return;
    }

    // Remember what we are on now, so we can come back to it.
    wifiPreviousSsid = WiFi.SSID();
    wifiPreviousPass = WiFi.psk();
    wifiLastError = "";
    wifiErrorDetail = "";
    wifiSwitchState = WIFI_SWITCH_START;

    debugI("WiFi switch requested: %s", wifiPendingSsid.c_str());
    server.send(200, "application/json", "{\"msg\":\"\"}");
}

// Drives the switch started by updateWifi(), including the fallback.
void handleWifiSwitch()
{
    switch (wifiSwitchState)
    {
        case WIFI_SWITCH_START:
        {
            WiFi.disconnect();
            WiFi.begin(wifiPendingSsid.c_str(), wifiPendingPass.c_str());
            wifiSwitchDeadline = millis() + WIFI_SWITCH_TIMEOUT;
            wifiSwitchState = WIFI_SWITCH_WAIT_NEW;
            break;
        }
        case WIFI_SWITCH_WAIT_NEW:
        {
            if (WiFi.status() == WL_CONNECTED)
            {
                debugI("WiFi switch done: %s", WiFi.SSID().c_str());
                wifiSwitchState = WIFI_SWITCH_IDLE;
                wifiConnected = true;
                wifiFirstConnected = true;  // re-init NTP and the servers
            }
            else if ((long)(millis() - wifiSwitchDeadline) >= 0)
            {
                debugW("WiFi switch failed, falling back to %s", wifiPreviousSsid.c_str());
                wifiLastError = "wifiConnect";
                wifiErrorDetail = wifiPendingSsid;
                WiFi.disconnect();
                WiFi.begin(wifiPreviousSsid.c_str(), wifiPreviousPass.c_str());
                wifiSwitchDeadline = millis() + WIFI_SWITCH_TIMEOUT;
                wifiSwitchState = WIFI_SWITCH_WAIT_OLD;
            }
            break;
        }
        case WIFI_SWITCH_WAIT_OLD:
        {
            if (WiFi.status() == WL_CONNECTED)
            {
                wifiSwitchState = WIFI_SWITCH_IDLE;
                wifiConnected = true;
                wifiFirstConnected = true;
            }
            else if ((long)(millis() - wifiSwitchDeadline) >= 0)
            {
                // Both networks are gone; the normal reconnect logic takes over.
                debugE("Fallback to %s failed too", wifiPreviousSsid.c_str());
                wifiLastError = "wifiFallback";
                wifiErrorDetail = wifiPreviousSsid;
                wifiSwitchState = WIFI_SWITCH_IDLE;
            }
            break;
        }
        default:
            break;
    }
}




/**
 * The two things worth writing about the brightness screen.
 *
 *   {forget: <n>}   drop one taught point, by its place in the list
 *   {reset: true}   drop all of them, the same as POST /light {reset}
 *
 * **Behind the lock, while GET /luminance is not.** Looking at a brightness
 * curve is what somebody does when the automatic feels wrong, and putting a
 * password in front of that would be a lock in the way of a diagnosis. Editing
 * it is a different act, and it is the one the screen only offers once the
 * clock is unlocked.
 *
 * Forgetting one point exists because a point can be wrong rather than merely
 * old, and until this the only remedy was throwing the whole calibration away.
 */
void updateLuminance()
{
    if (!Expert::guard()) return;

    JsonDocument doc;
    deserializeJson(doc, server.arg(0));

    if (doc["reset"] | false)
    {
        Luminance::reset();
        needsUpdateFromRtc = true;
        sendLuminance();
        return;
    }

    // Both ends of the regulated range. How dim a face is still readable
    // depends on the panel, the distance and the eyes, so 20 % was never a
    // constant of nature - it was one clock's answer.
    if (!doc["minPercent"].isNull() || !doc["maxPercent"].isNull())
    {
        uint8_t low  = doc["minPercent"] | Luminance::minPercent();
        uint8_t high = doc["maxPercent"] | Luminance::maxPercent();
        if (!Luminance::setRange(low, high))
        {
            server.send(400, "application/json", "{\"error\":\"lumRange\"}");
            return;
        }
        needsUpdateFromRtc = true;
        sendLuminance();
        return;
    }

    if (doc["forget"].is<int>())
    {
        int index = doc["forget"].as<int>();
        if (index < 0 || !Luminance::forget((uint8_t)index))
        {
            server.send(404, "application/json", "{\"error\":\"lumNoSuchPoint\"}");
            return;
        }
        needsUpdateFromRtc = true;
        sendLuminance();
        return;
    }

    // One colour correction, by its place in `user.residuals`. The same
    // argument as forgetting a white point: a correction can be wrong rather
    // than merely old - made ten seconds after somebody turned a lamp off -
    // and the only remedy before this was throwing all of them away.
    if (doc["forgetResidual"].is<int>())
    {
        int index = doc["forgetResidual"].as<int>();
        if (index < 0 || !Luminance::forgetResidual((uint8_t)index))
        {
            server.send(404, "application/json", "{\"error\":\"lumNoSuchPoint\"}");
            return;
        }
        needsUpdateFromRtc = true;
        sendLuminance();
        return;
    }

    /*
     * Back to the factory baseline.
     *
     * What goes: the colour corrections, and the white points that are the
     * same preferences said in the old coordinates. What stays: the **coupling
     * measurement**, which is twenty minutes of the clock measuring where its
     * own sensor sits behind its own letters and has nothing to do with
     * anybody's taste. Throwing that away with the preferences would be the
     * one irreversible part of an otherwise cheap reset.
     *
     * Refused when there is no valid profile to restore *to*, and refused
     * before anything in NVS is touched: a restore that failed half way would
     * leave the clock between two models, which is a state nothing here can
     * describe.
     */
    if (doc["factoryRestore"] | false)
    {
        if (!Luminance::factoryRestore())
        {
            server.send(409, "application/json", "{\"error\":\"factoryUnavailable\","
                        "\"errorDetail\":\"there is no valid factory profile to "
                        "restore to\"}");
            return;
        }
        needsUpdateFromRtc = true;
        sendLuminance();
        return;
    }

    server.send(400, "application/json", "{\"error\":\"calibrationRange\"}");
}

/** Reset reasons, short enough to put in a table cell and specific enough to matter. */
static const char *resetReasonName()
{
    switch (esp_reset_reason())
    {
        case ESP_RST_POWERON:  return "power-on";
        case ESP_RST_EXT:      return "external";
        case ESP_RST_SW:       return "software";    // our own ESP.restart()
        case ESP_RST_PANIC:    return "panic";       // the interesting one
        case ESP_RST_INT_WDT:  return "watchdog-int";
        case ESP_RST_TASK_WDT: return "watchdog-task";
        case ESP_RST_WDT:      return "watchdog";
        case ESP_RST_BROWNOUT: return "brownout";    // the other interesting one
        case ESP_RST_SDIO:     return "sdio";
        case ESP_RST_DEEPSLEEP: return "deep-sleep";
        // The five below are ESP32-S3 additions, and leaving them out is how
        // this first reported "unknown" for the most ordinary restart there
        // is: a XIAO has no USB-serial converter, so the reset that ends a
        // flash comes from the chip's own USB peripheral and lands on
        // ESP_RST_USB. CPU_LOCKUP is the double exception - worth telling
        // apart from a plain panic, since it usually means the panic handler
        // itself fell over.
        case ESP_RST_USB:        return "usb";
        case ESP_RST_JTAG:       return "jtag";
        case ESP_RST_EFUSE:      return "efuse";
        case ESP_RST_PWR_GLITCH: return "power-glitch";
        case ESP_RST_CPU_LOCKUP: return "cpu-lockup";
        default:               return "unknown";
    }
}

/** Appends a string as a JSON string literal, quotes and all. */
static void appendJsonString(String &out, const char *text)
{
    out += '"';
    for (const char *at = text; *at; at++)
    {
        unsigned char c = (unsigned char)*at;
        if (c == '"' || c == '\\')
        {
            out += '\\';
            out += (char)c;
        }
        else if (c < 0x20)
        {
            // Should not occur - the ring stores whole lines with the control
            // characters already taken out - but a JSON document with a raw
            // control character in it is not JSON, and the tab would show
            // nothing at all rather than one odd line.
            char escaped[7];
            snprintf(escaped, sizeof(escaped), "\\u%04x", c);
            out += escaped;
        }
        else
        {
            out += (char)c;   // UTF-8 passes through; JSON is UTF-8
        }
    }
    out += '"';
}

/**
 * The clock's log, and enough of its state to know what it was doing.
 *
 * Polled by the debug tab with the sequence number it last saw, so the usual
 * answer carries nothing but the handful of lines that have appeared since.
 * A freshly opened tab asks with `since=0` and gets the oldest batch first;
 * `more` then says whether another round is worth it, which is what fills the
 * window with the boot in one go rather than one screen every two seconds.
 *
 * `oldest` is not decoration: it says which line the ring still starts at, so
 * the browser can tell "nothing new" from "the ring wrapped and you missed
 * 300 lines". Dropping that silently is exactly what makes a log window
 * untrustworthy.
 *
 * Built into one String with the room reserved up front rather than through
 * ArduinoJson: a hundred lines would put every one of them into a document
 * first and serialise that into a second buffer, and this runs on the same
 * heap an update wants.
 */
void sendLog()
{
    // The log is behind the lock: it carries whatever the clock has said about
    // itself, and that is not for everyone who can reach port 80.
    if (!Expert::guard()) return;

    uint32_t since = 0;
    if (server.hasArg("since")) since = strtoul(server.arg("since").c_str(), nullptr, 10);

    static Log::Line batch[LOG_BATCH];
    size_t count = Log::collect(since, batch, LOG_BATCH);

    uint32_t oldest = Log::oldestSeq();
    uint32_t next = Log::nextSeq();
    // What the caller should ask for next time. With nothing to send that is
    // where it already stood - clamped to the ring, so a restart hands back a
    // smaller number than was asked for instead of one that never comes round.
    uint32_t served = since;
    if (count > 0)        served = batch[count - 1].seq + 1;
    else if (served < oldest) served = oldest;
    else if (served > next)   served = next;

    String out;
    out.reserve(count * (LOG_LINE_MAX + 40) + 400);

    out += "{\"oldest\":";  out += oldest;
    out += ",\"seq\":";     out += served;
    out += ",\"more\":";    out += (served < next) ? "true" : "false";

    // What to look at first when something has gone wrong, and cheap enough to
    // send on every poll. The heap numbers are here because they are the ones
    // the intermittent "could not activate the firmware" points at.
    out += ",\"uptime\":";  out += millis();
    out += ",\"heap\":";    out += ESP.getFreeHeap();
    out += ",\"heapMin\":"; out += ESP.getMinFreeHeap();
    out += ",\"heapBlock\":"; out += ESP.getMaxAllocHeap();
    out += ",\"reset\":\""; out += resetReasonName(); out += '"';

    out += ",\"lines\":[";
    for (size_t i = 0; i < count; i++)
    {
        if (i > 0) out += ',';
        out += "{\"s\":";  out += batch[i].seq;
        out += ",\"t\":";  out += batch[i].ms;
        out += ",\"l\":";  out += batch[i].level;
        out += ",\"m\":";
        appendJsonString(out, batch[i].text);
        out += '}';
    }
    out += "]}";

    server.send(200, "application/json", out);
}


/**
 * Whether the clock is unlocked, and what it would take to unlock it.
 *
 * Carries no secret: the flag, whether a password has ever been set, and how
 * long the reset window is still open. The web UI needs all three before it
 * can decide between "enter your password", "choose one" and "you have five
 * minutes to start over".
 */
void sendExpert()
{
    JsonDocument doc;
    doc["enrolled"]  = Expert::enrolled();
    doc["unlocked"]  = Expert::unlocked();
    doc["grace"]     = Expert::graceRemaining();
    doc["lockedOut"] = Expert::lockedOut();

    String out;
    serializeJson(doc, out);
    server.send(200, "application/json", out);
}

/**
 * Sets, checks or clears the password.
 *
 *   {password}       on a clock with none: stores it and unlocks
 *                    otherwise: unlocks if it matches
 *   {off: true}      locks again - no password needed, see Expert.h
 *   {reset: true}    forgets the password, only inside the grace window
 *
 * Answers with the same shape GET does, so the UI has the new state without a
 * second request, or with a code from the err_* set.
 */
void updateExpert()
{
    JsonDocument doc;
    deserializeJson(doc, server.arg(0));

    if (doc["off"] | false)
    {
        Expert::lock();
        sendExpert();
        return;
    }

    if (doc["reset"] | false)
    {
        if (!Expert::reset())
        {
            server.send(403, "application/json", "{\"error\":\"expertNoGrace\"}");
            return;
        }
        sendExpert();
        return;
    }

    const char *password = doc["password"] | "";

    if (Expert::lockedOut())
    {
        server.send(429, "application/json", "{\"error\":\"expertLockedOut\"}");
        return;
    }

    // Enrolling and unlocking are the same request on purpose. Which one it is
    // depends on the clock, not on what the browser believes about it, and a
    // browser holding a stale answer would otherwise ask for the wrong one.
    bool ok = Expert::enrolled() ? Expert::unlock(password) : Expert::enroll(password);

    if (!ok)
    {
        // "Too short" is only meaningful while enrolling; afterwards saying it
        // would tell whoever is guessing how long the real one is.
        const char *code = Expert::enrolled() ? "expertWrongPassword" : "expertPasswordShort";
        server.send(403, "application/json", String("{\"error\":\"") + code + "\"}");
        return;
    }

    sendExpert();
}


/**
 * Every language this firmware can render, in the order of the numbers stored
 * in NVS - so the index in the array is the value to POST to /configuration.
 *
 * The names used to live in the web UI, ten of them in each of six locale
 * files, in an order that had to agree with the LANGUAGE_* defines without
 * anything checking that it did. Adding a language cost one file here and six
 * there. It costs one file here now: `name` and `uiLocale` have always been
 * part of a Language, this is only the endpoint that hands them over.
 *
 * `panel` groups the ones cut into the same sheet of letters: it is the number
 * of the first language using that panel, so German, Swabian, Bavarian and
 * Saxon all report 0 and Italian reports itself. A clock has exactly one panel
 * and no setting changes that, so outside expert mode the picker offers only
 * the group the clock is already in - see updateConfiguration(), which is
 * where it is actually enforced.
 *
 * The grouping is worked out from the letters every time rather than stored
 * beside them, because a stored group number would be the same fact written
 * twice and the two would drift.
 *
 * Static for a given firmware - the lock state is deliberately *not* folded in
 * here - so the browser asks once and does not poll. It is deliberately not
 * part of /currentState, which is settings.
 */
void sendLanguages()
{
    JsonDocument doc;
    JsonArray list = doc.to<JsonArray>();

    for (byte i = 0; i < LANGUAGE_COUNT; i++)
    {
        const Language *language = Languages::find(i);
        if (language == nullptr) continue;   // a gap in the table, not an error

        byte panel = i;
        for (byte j = 0; j < i; j++)
        {
            if (Languages::samePanel(Languages::find(j), language)) { panel = j; break; }
        }

        JsonObject entry = list.add<JsonObject>();
        entry["value"]    = i;
        entry["code"]     = language->code;
        entry["name"]     = language->name;
        entry["uiLocale"] = language->uiLocale;
        entry["panel"]    = panel;
    }

    String out;
    serializeJson(doc, out);
    server.send(200, "application/json", out);
}


/**
 * The face, as it is at this moment.
 *
 * Both halves come out of the same place the LEDs do: `rows` is the panel of
 * the language that is running, `on` is read straight off the frame buffer.
 * That is the whole point - the browser is not a second opinion about what the
 * clock ought to be showing, it shows what the clock *is* showing, a wrong
 * render included. Rebuilding the grammar in JavaScript would have been a
 * second implementation to keep in step, and it would have hidden exactly the
 * faults worth seeing.
 *
 * `on` is written as `#` and `.` rather than as a bit mask so that the answer
 * can be read with curl: two aligned grids, the letters and what is lit.
 *
 * The four corners are reported separately, in reading order rather than in
 * the order the strip is soldered. Which row is which corner is written down
 * at Renderer::setCorners, and comes from the clock rather than from the code:
 * following the pixel remapping through the driver gives the wrong answer.
 *
 * With the coloured corners switched on they are not in the display colour at
 * all - the newest one walks the hue wheel with the seconds - so `cornerColors`
 * carries what each is actually showing. The browser cannot work that out and
 * must not try: it asks the driver, through here. The colours are the pure hue
 * at full value; how bright the clock is running is the preview's own business,
 * as it already is for the letters.
 *
 * The field is absent, not empty, when the mode is off. An older web UI then
 * behaves exactly as it did, and a newer one can tell "no colours" from "four
 * dark corners" without a second flag.
 */
void sendPanel()
{
    const Language *language = Languages::find(settings.getLanguage());
    if (language == nullptr)
    {
        server.send(404, "application/json", "{\"error\":\"noPanel\"}");
        return;
    }

    JsonDocument doc;
    doc["language"] = settings.getLanguage();
    doc["code"]     = language->code;
    doc["name"]     = language->name;
    doc["uiLocale"] = language->uiLocale;
    doc["mode"]     = mode;

    JsonArray rows = doc["rows"].to<JsonArray>();
    JsonArray on   = doc["on"].to<JsonArray>();
    for (uint8_t row = 0; row < PANEL_ROWS; row++)
    {
        rows.add(language->rows[row]);

        char lit[PANEL_COLS + 1];
        for (uint8_t col = 0; col < PANEL_COLS; col++)
        {
            lit[col] = (matrix[row] & (1 << (15 - col))) ? '#' : '.';
        }
        lit[PANEL_COLS] = '\0';
        on.add(lit);
    }

    // Reading order: top left, top right, bottom right, bottom left.
    const uint8_t CORNER_ROW[4] = { 1, 0, 3, 2 };
    JsonArray corners = doc["corners"].to<JsonArray>();
    for (uint8_t i = 0; i < 4; i++)
    {
        corners.add((matrix[CORNER_ROW[i]] & 0b11111) == 0b11111);
    }

    if (settings.getRenderColorCorner() && mode == STD_MODE_NORMAL)
    {
        JsonArray colors = doc["cornerColors"].to<JsonArray>();
        for (uint8_t i = 0; i < 4; i++)
        {
            byte hue;
            if (!ledDriver.cornerHue(i, hue))
            {
                colors.add("");
                continue;
            }

            // hsv2rgb_rainbow, not a plain HSV conversion: FastLED's wheel is
            // deliberately not the geometric one, and the preview should show
            // the colour the LED shows.
            CRGB rgb;
            hsv2rgb_rainbow(CHSV(hue, 255, 255), rgb);

            char hex[8];
            snprintf(hex, sizeof(hex), "#%02x%02x%02x", rgb.r, rgb.g, rgb.b);
            colors.add(hex);
        }
    }

    // The same sentence the once-a-minute log line carries, so the browser can
    // put it under the panel without walking the grid again.
    doc["text"] = displayedWords(settings.getLanguage());

    String out;
    serializeJson(doc, out);
    server.send(200, "application/json", out);
}


// ------ the interface the rest of the program sees ------

void Web::begin()
{
    // Anything not matched below is looked for in the filesystem, which is
    // where the web UI itself lives.
    server.onNotFound([]()
    {
        if (!Web::serveFromFilesystem(server.uri()))
        {
            server.send(404, "text/plain", "404: Not Found");
        }
    });

    // Answers cross-origin so the Vite dev server can drive a real clock.
    server.enableCORS();

    server.on("/currentState", sendCurrentState);
    server.on("/color", updateColor);
    server.on("/display", updateDisplay);
    server.on("/autoluminance", updateAutoLuminance);
    server.on("/configuration", updateConfiguration);
    server.on("/timezone", updateTimezone);
    server.on("/light", HTTP_GET, sendLight);
    server.on("/panel", HTTP_GET, sendPanel);
    server.on("/languages", HTTP_GET, sendLanguages);
    server.on("/luminance", HTTP_GET, sendLuminance);
    server.on("/luminance", HTTP_POST, updateLuminance);
    // Open, like GET /luminance beside it and for the same reason: it is the
    // diagram, and a password in front of a diagnosis helps nobody.
    server.on("/luminance/surface", HTTP_GET, sendLuminanceSurface);
    server.on("/light", HTTP_POST, updateLight);
    server.on("/manifest.webmanifest", HTTP_GET, sendManifest);
    server.on("/hostname", HTTP_POST, updateHostname);
    server.on("/restart", HTTP_POST, restartClock);
    server.on("/wifi", HTTP_GET, sendWifiStatus);
    server.on("/wifi", HTTP_POST, updateWifi);
    server.on("/wifi/scan", HTTP_GET, sendWifiScan);
    server.on("/log", HTTP_GET, sendLog);
    server.on("/expert", HTTP_GET, sendExpert);
    server.on("/expert", HTTP_POST, updateExpert);
}

void Web::poll()
{
    handleWifiSwitch();
}

bool Web::switchingNetwork()
{
    return wifiSwitchState != WIFI_SWITCH_IDLE;
}
