FranzKugler/QlockThreeW32/src/Calibration.cpp

/**
 * Calibration - see Calibration.h for the three passes and why they are needed.
 */
#include "Calibration.h"
#include "Coupling.h"
#include "DisplayModes.h"
#include "LedDriverWS2812FastLED.h"
#include "LightSensor.h"
#include "LogBuffer.h"
#include "LabRoutes.h"

#include <ArduinoJson.h>

#define CAL_TASK_STACK 8192

// The drive levels the response table is sampled at, descending. Below 4 the
// contribution is under half a per cent of full and the counts are noise, so
// the table stops there and anything smaller is interpolated down to zero.
static const uint8_t DRIVE_LEVELS[] = { 255, 192, 128, 96, 64, 48, 32, 24, 16, 12, 8, 6, 4 };
#define DRIVE_STEPS ((uint8_t)(sizeof(DRIVE_LEVELS) / sizeof(DRIVE_LEVELS[0])))

#define ROWS 10
#define COLUMNS 11
#define CELL_COUNT (ROWS * COLUMNS)

extern LedDriverWS2812FastLED ledDriver;
extern AmbientLight ambientLight;
extern byte mode;
extern bool needsUpdateFromRtc;

namespace
{
    TaskHandle_t task = nullptr;

    volatile bool active = false;
    volatile bool stopWanted = false;
    volatile uint8_t phase_ = Calibration::IDLE;
    volatile uint16_t done_ = 0;
    volatile uint16_t total_ = 0;
    volatile float ambient_ = 0.0f;
    volatile uint8_t rung_ = 0;
    volatile uint8_t kept_ = 0;
    char error_[32] = "";

    byte modeBefore = STD_MODE_NORMAL;

    // The coarse pass, out of the task's stack: 110 floats is not a lot, but it
    // sits beside an ArduinoJson document and a FreeRTOS stack is not the heap.
    float coarse[CELL_COUNT];
    uint8_t keptRow[COUPLING_MAX_CELLS];
    uint8_t keptCol[COUPLING_MAX_CELLS];
    float keptRed[COUPLING_MAX_CELLS];
    float keptGreen[COUPLING_MAX_CELLS];
    float keptBlue[COUPLING_MAX_CELLS];
    float driveResponse[DRIVE_STEPS];

    void fail(const char *code)
    {
        strncpy(error_, code, sizeof(error_) - 1);
        error_[sizeof(error_) - 1] = '\0';
        phase_ = Calibration::FAILED;
    }

    void step(uint8_t phase, uint16_t total)
    {
        phase_ = phase;
        done_ = 0;
        total_ = total;
    }

    // ------ the strip ------

    void show()
    {
        ledDriver.showRaw();
        vTaskDelay(pdMS_TO_TICKS(CAL_SETTLE_MS));
    }

    void dark()
    {
        ledDriver.clearRaw();
        show();
    }

    void light(uint8_t row, uint8_t column, uint8_t r, uint8_t g, uint8_t b)
    {
        ledDriver.clearRaw();
        byte pixel = LedDriverWS2812FastLED::physicalFor(row, column);
        if (pixel != 255) ledDriver.setPixelRaw(pixel, CRGB(r, g, b));
        show();
    }
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
